sztvka/nixie_clock/stm32/stm32f411ccu6tr/Src/nixie.c

//
// Created by sztuka on 17.03.2023.
//
#include "nixie.h"


void setNixieTime(Nixie_Clock* clock, RTC_TimeTypeDef* time) {
    setNixie(clock->tubes[0], (uint8_t)time->Hours/10);
    setNixie(clock->tubes[1], (uint8_t)time->Hours%10);
    setNixie(clock->tubes[2], (uint8_t)time->Minutes/10);
    setNixie(clock->tubes[3], (uint8_t)time->Minutes%10);
}

void NixieShuffle(Nixie_Clock* clock) {
    uint8_t previousValues[4];
    for (int i = 0; i < 4; i++) {
        previousValues[i] = clock->tubes[i]->value;
    }
    for (int i = 0; i < 10; i++) {
        for(int b = 0; b<4; b++){
            setNixie(clock->tubes[b], i);
        }
        HAL_Delay(200);
    }
    for (int i = 0; i < 4; i++) {
        setNixie(clock->tubes[i], previousValues[i]);
    }
}

void setNixie(Nixie_IC* nixie, uint8_t value) {
    if(value>9) value = 15; // if value greater than 9 turn off nixie to signal error
    nixie->value = value;
    for (int i = 0; i < 4; i++) {
        // (value>>i)&1 walks through the bits of value
        GPIO_PinState state = ((value>>i)&1)==1 ? GPIO_PIN_SET: GPIO_PIN_RESET;
        HAL_GPIO_WritePin(nixie->ports[i].port, nixie->ports[i].pin, state);
    }
}

void disableNixie(Nixie_IC* nixie) {
    for (int i = 0; i < 4; i++) {
        HAL_GPIO_WritePin(nixie->ports[i].port, nixie->ports[i].pin, GPIO_PIN_SET);
    }
}
